sebastienroy/mamemasradio/documentation/pictures/fullres/3layers.jpg

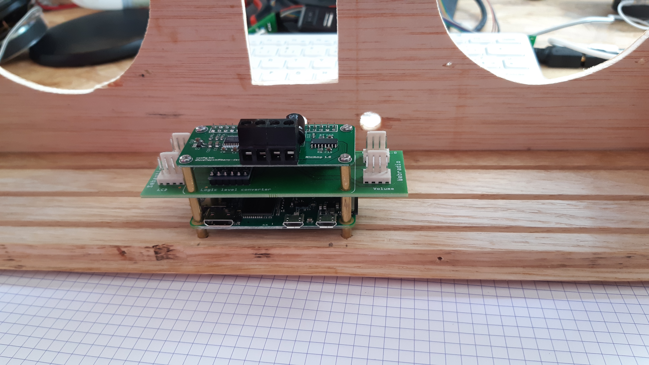
documentation/pictures/fullres/3layers.jpg
