sebastienroy/mamemasradio/documentation/pictures/fullres/inside_box.jpg

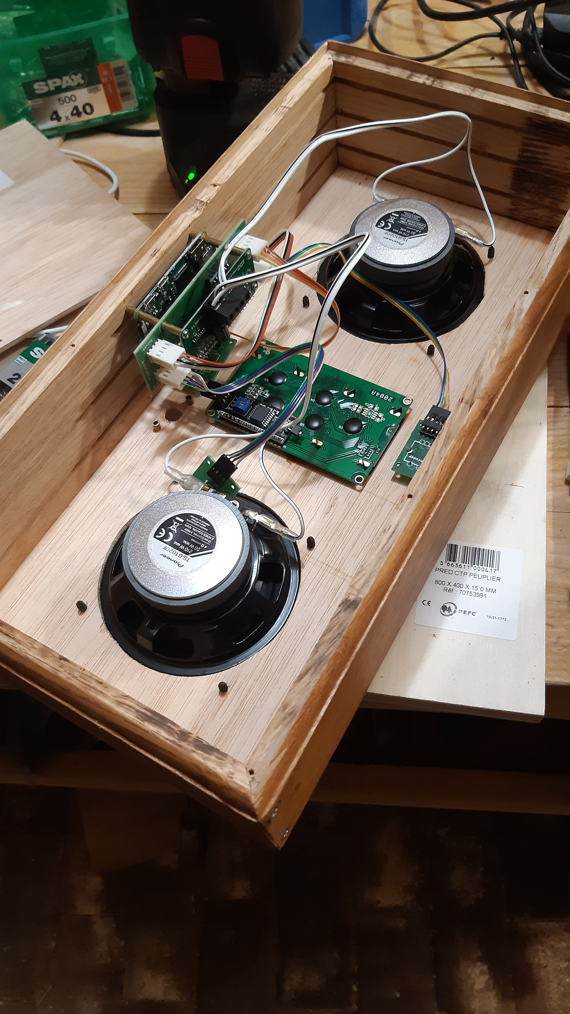
documentation/pictures/fullres/inside_box.jpg
