sebastienroy/mamemasradio/documentation/pictures/fullres/radio_front_off.jpg

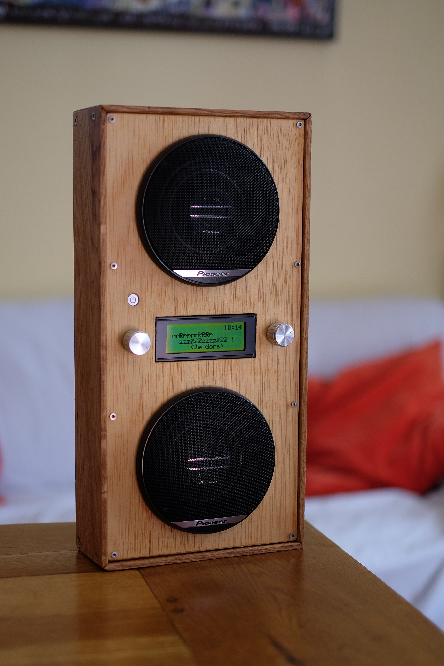
documentation/pictures/fullres/radio_front_off.jpg
