sebastienroy/mamemasradio/pcb_design/breadboard.png

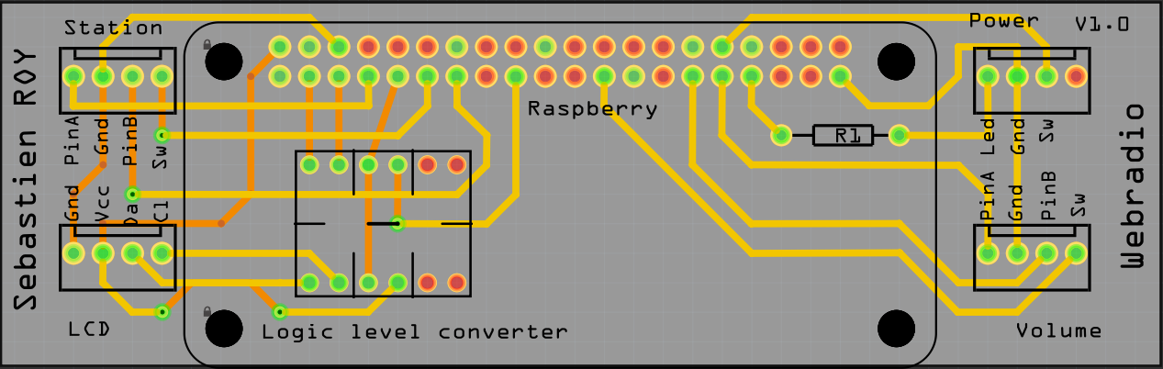
pcb_design/breadboard.png
