sebastienroy/mamemasradio/pcb_design/parts/PowerSwitch-part/HTB1JPCuRFXXXXcoXFXXq6xXFXXX3.jpg

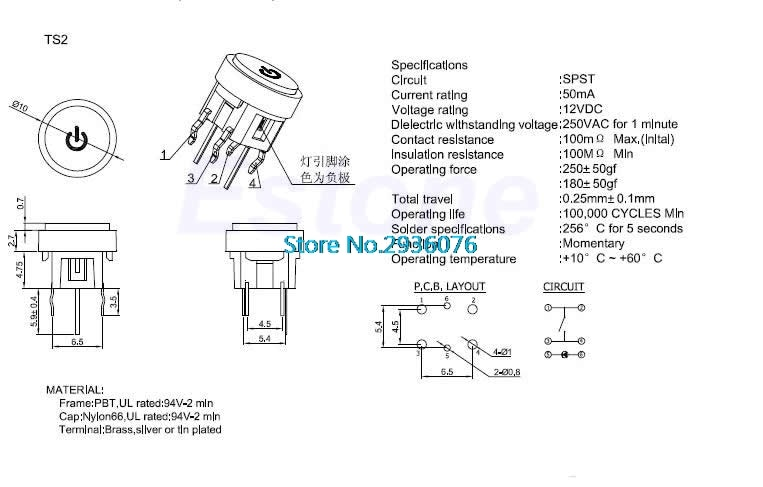
pcb_design/parts/PowerSwitch-part/HTB1JPCuRFXXXXcoXFXXq6xXFXXX3.jpg
