sebastienroy/mamemasradio/python/radiostate.py

#!/usr/bin/env python3
# -*- coding: utf-8 -*-
"""
Created on Sun Sep 23 15:15:25 2018

@author: Sebastien Roy
"""

class RadioState:
    def __init__(self, context, owner):
        self._ctxt = context
        self._owner = owner
        return

    def enter_state(self):
        return

    def leave_state(self):
        return

    def handle_event(self, event):
        return

    def cleanup(self):
        return
